chuangzhu/float-watch/firm/FloatWatch/APP_Display.h

/*
 * APP_Display.h
 *
 * Created: 2017/10/14 7:21:48
 *  Author: geneLocated
 */ 


#ifndef APP_DISPLAY_H_
#define APP_DISPLAY_H_

#include <avr/io.h>
#include "APP_Clock.h"

void comReg(unsigned char Data);

void displayTime(void);

extern unsigned char disStatus;

#endif /* APP_DISPLAY_H_ */
