chuangzhu/float-watch/firm/FloatWatch/F_CPU.h

/*
 * F_CPU.h
 * 请在此处定义F_CPU
 * Created: 2017/10/4 10:38:51
 *  Author: geneLocated
 */ 


#ifndef F_CPU_H_
#define F_CPU_H_

#define F_CPU	8000000
#define baud	9600
#define TIMER0_Period	1000
#define TIMER2_Period	10000

#endif /* F_CPU_H_ */
